Scott216/Leak_Detector_obsolete/Photos/Leak_Detector 1.jpg

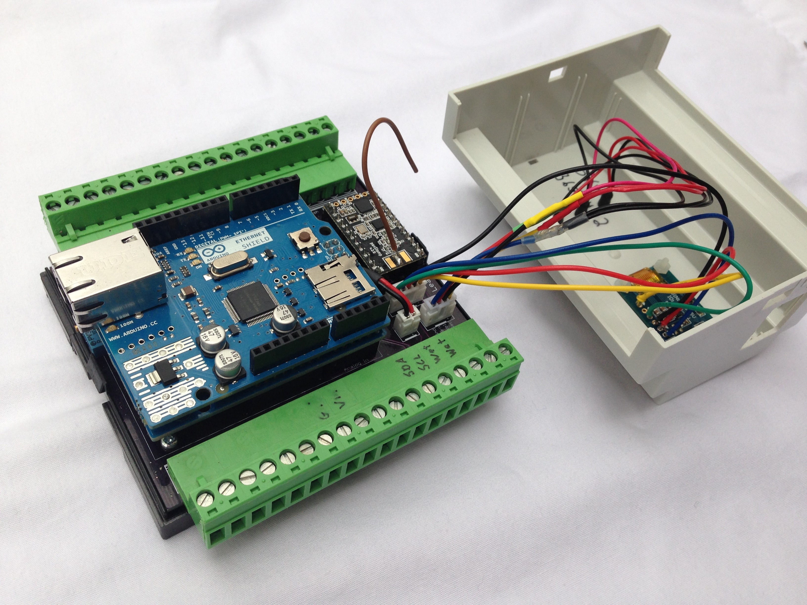
Photos/Leak_Detector 1.jpg
