Scott216/Leak_Detector_obsolete/Water_Detector_Main/Water_Detector_Main/Water_Detector_Main_Library.cpp

//
// Water_Detector_MainLibrary.cpp 
// Library C++ code
// ----------------------------------
// Developed with embedXcode+ 
// http://embedXcode.weebly.com
//
// Project 		Water_Detector_Main Library
//
// Created by 	Scott Goldthwaite, 1/24/14 10:36 AM
// 				Scott Goldthwaite
//
// Copyright 	© Scott Goldthwaite, 2014
// License		GNU General Public License
//
// See 			Water_Detector_MainLibrary.cpp.h and ReadMe.txt for references
//


#include "Water_Detector_Main_Library.h"
